robusnagus/DCCdecoder/funcdec_proto3208.X/dec08_config.h

//
// Project: DCC decoder proto M3208
// File:    dec08_config.h
// Author:  Nagus
// Version: 20191229
//

#ifndef DEC08_CONFIG_H
#define	DEC08_CONFIG_H

#define SER_BRATE				115200
#define SER_TX_DATASIZE         64
#define SER_RX_DATASIZE         64

#define CFG_DCCR_ONEBTIME       870
#define CFG_DCCR_PREAMBMIN      11
#define CFG_DCCR_PKTMAXLEN      6

#endif	// DEC08_CONFIG_H
